BoujeeEnjinia1701/pvtrace/cad/drawings/PVT-DWG-001.pdf

CONCEPT, NOT FOR FABRICATION | PVTrace · github.com/BoujeeEnjinia1701/pvtrace

FRONT VIEW
Scale 1:5; looking at the front (along +Y)

TOP VIEW
Scale 1:5; looking down (along -Z)

RIGHT VIEW
Scale 1:5; looking at the right side (along -X)

320

144 98

ISOMETRIC VIEW
Not to scale; seen from the front right and above, about 30 deg elevation

KEY DIMENSIONS AND INTERFACES (MM)
Case 220 x 130 x 80; 234 x 144 over bumpers
Wall 3; parting line Z 52; knob and hood top Z 98
+X end: 2 x M16 glands at Y +/-18, Z 30, test leads 4 mm2 -X end: M12 sensor gland Y 45; USB-C socket Y 22 Chassis plate PC 1.5 on five 5 mm standoffs
Load: 3 x 2200 uF 160 V, 6.6 mF, 2 cable ties
Isolation board between measurement side and controller
Lid: 3-key membrane keypad and two status LEDs, controller side Window 72 x 54 bonded over 62 x 46 opening
Display board on 4 spacers; hood screws hold both
Rating 100 V DC, 20 A; 20 A gPV fuse; 2-pole DC isolator
Stored energy up to 33 J; dump 22 ohm, bleed 10 kohm Mass about 1.49 kg with leads and pod (PVT-CAL-001) Making sketches PVT-DWG-101 to 108 (lid: 104) PRELIMINARY, NOT FOR FABRICATION
REV | DESCRIPTION | DATE | BY
P1 | Preliminary GA, 6.6 mF and isolation barrier (PVT-DDR-001) | 2026-09-25 | AC
P2 | Display sun hood added (PVT-DDR-002) | 2026-09-25 | AC
P3 | Constructable design: plate, fixings, USB-C (PVT-DDR-003) | 2026-10-01 | AC
P4 | Keypad and status LEDs on the lid (PVT-DEC-001 item 6) | 2026-10-02 | AC
PVTRACE | github.com/BoujeeEnjinia1701/pvtrace

## General arrangement, handheld tracer

DRAWING NO.
PVT-DWG-001

REV
P4

SHEET
1 of 1

SIZE

## ANSI B

SCALE
1:5

UNITS
mm
PROJECTION | DATE
2026-10-02

DRAWN
Amish Chadha

MATERIAL / NOTES
Case IP54 ABS, light grey; window and chassis plate PC; hood PETG. See bom/bom.csv, PVT-CAL-001
Licensed CERN-OHL-S-2.0 · Design Molecule Lab · designmolecule.com | Generated from cad/src; do not edit by hand
