BoujeeEnjinia1701/pvtrace/cad/drawings/PVT-DWG-101.pdf

### BUILD PLAN SKETCH, PLAN NOT YET BUILT PVTrace · github.com/BoujeeEnjinia1701/pvtrace

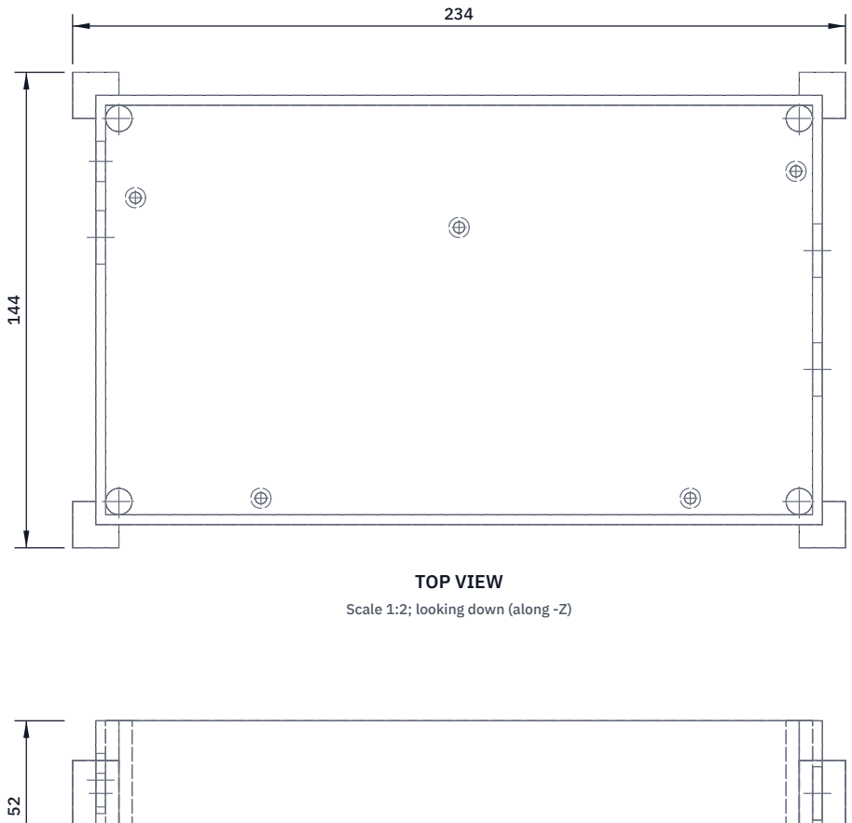
[picture p39: figure]
TOP VIEW; Scale 1:2; looking down (along -Z)

FRONT VIEW
Scale 1:2; looking at the front (along +Y)

RIGHT VIEW
Scale 1:2; looking at the right side (along -X)

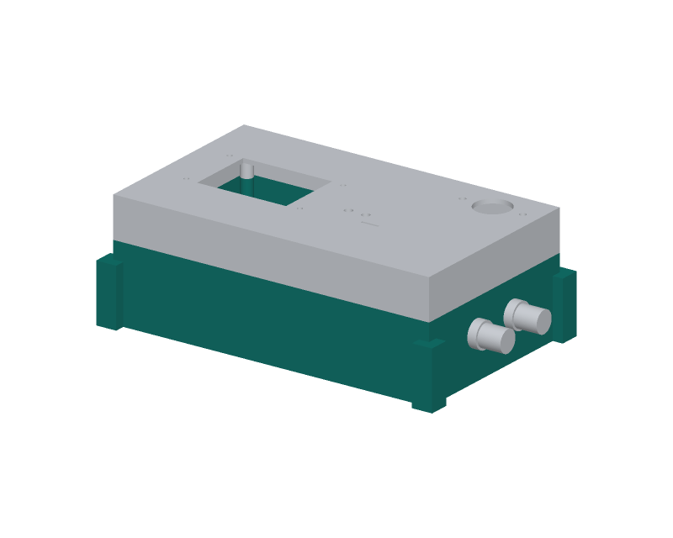
[picture p40: figure]

WHERE IT GOES
This part in colour, its neighbours in grey

HOW TO MAKE IT AND HOW IT FITS
Drill the body only. Front is the long side toward the user; right is
the end the test leads leave from. Sizes from outside faces.
Right end: two 16.2 mm holes for the M16 lead glands, 47 and 83 mm from the front face, 30 mm up from the bottom.
Left end: 16.2 mm hole for the USB-C socket, 87 mm from the front face, 34 mm up; 12.2 mm hole for the M12 sensor gland, 110 mm from the front face, 30 mm up.
Floor: five 3.4 mm holes, countersunk from below for M3 screws, at the positions on the case hole layout (from the left end and front face). Tape each face, pilot drill 2 mm with wood behind, open with a step drill at low speed. Deburr inside and out.
Check: the glands, socket and plate standoffs fit their holes.
REV | DESCRIPTION | DATE | BY
P1 | Making sketch for the prototype build plan | 2026-10-02 | AC
PVTRACE | github.com/BoujeeEnjinia1701/pvtrace

## PVTrace enclosure body: drilling sketch

DRAWING NO.
PVT-DWG-101

REV
P1

SHEET
1 of 1

SIZE

## ANSI B

SCALE
1:2

UNITS
mm
PROJECTION | DATE
2026-10-02

DRAWN
Amish Chadha

MATERIAL / NOTES
Bought IP54 ABS handheld case 220 x 130 x 80 mm, light grey
Licensed CERN-OHL-S-2.0 · Design Molecule Lab · designmolecule.com | Generated from cad/src; do not edit by hand
