BoujeeEnjinia1701/pvtrace/cad/drawings/PVT-DWG-102.pdf

### BUILD PLAN SKETCH, PLAN NOT YET BUILT PVTrace · github.com/BoujeeEnjinia1701/pvtrace

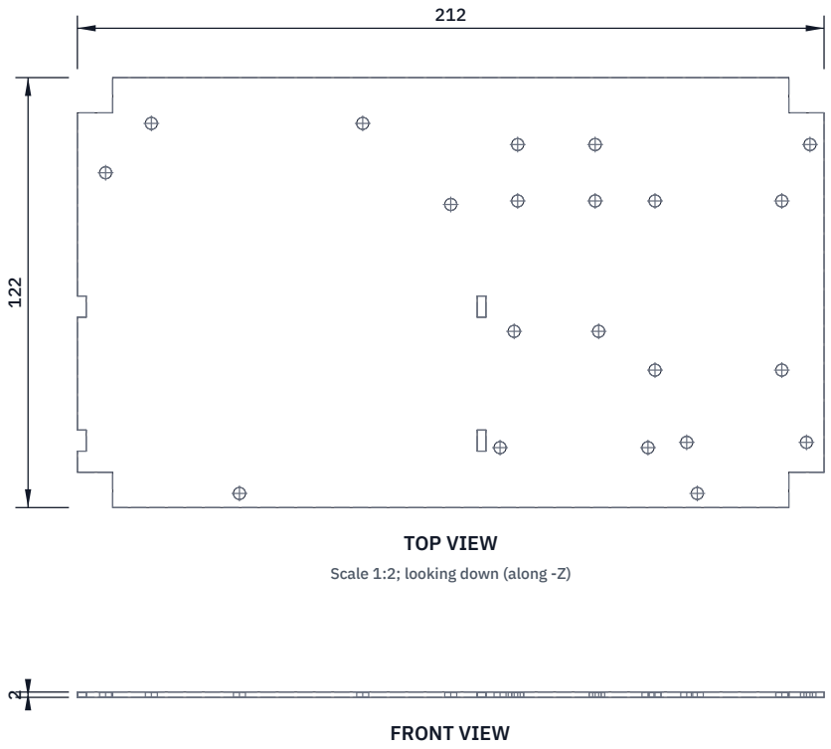
[picture p41: figure]
FRONT VIEW; TOP VIEW; Scale 1:2; looking down (along -Z)

Scale 1:2; looking at the front (along +Y)

RIGHT VIEW
Scale 1:2; looking at the right side (along -X)

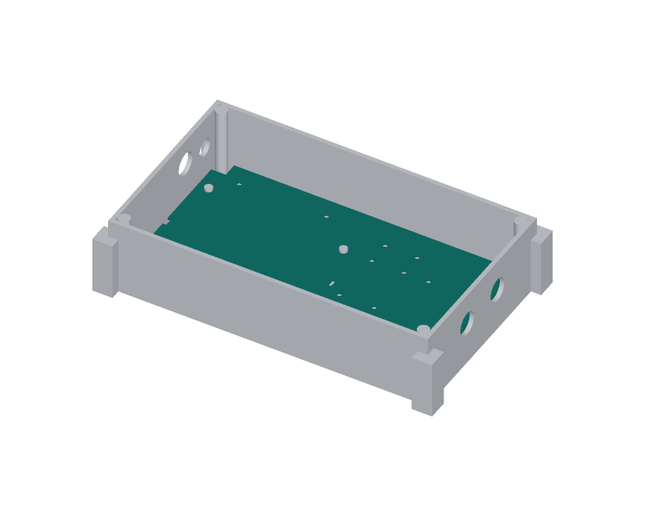
[picture p42: figure]

WHERE IT GOES
This part in colour, its neighbours in grey

HOW TO MAKE IT AND HOW IT FITS
Cut a 212 x 122 mm blank from 1.5 mm polycarbonate; keep the film on. Cut a 10 x 10 mm notch at each corner (clears the lid screw pillars).
Cut four cable tie slots, 2.5 x 6 mm: two open notches on the left edge and two slots 113.5 to 116 mm from the left edge; all four centred
19 and 57 mm from the front edge.
Drill the 21 holes 3.4 mm at the positions on the plate hole layout: five for the standoffs, the rest for the parts on the plate.
Score and snap or saw with a fine blade; file the edges smooth. Fit: the plate sits on five 5 mm standoffs, 1 mm in from every wall. Every part is screwed to the plate before it goes into the case. Check: lay it in the case; it drops in flat past the corner pillars.
REV | DESCRIPTION | DATE | BY
P1 | Making sketch for the prototype build plan | 2026-10-02 | AC
PVTRACE | github.com/BoujeeEnjinia1701/pvtrace

## PVTrace chassis plate: making sketch

DRAWING NO.
PVT-DWG-102

REV
P1

SHEET
1 of 1

SIZE

## ANSI B

SCALE
1:2

UNITS
mm
PROJECTION | DATE
2026-10-02

DRAWN
Amish Chadha

MATERIAL / NOTES
Polycarbonate sheet 1.5 mm, clear
Licensed CERN-OHL-S-2.0 · Design Molecule Lab · designmolecule.com | Generated from cad/src; do not edit by hand
