BoujeeEnjinia1701/pvtrace/cad/drawings/PVT-DWG-103.pdf

### BUILD PLAN SKETCH, PLAN NOT YET BUILT PVTrace · github.com/BoujeeEnjinia1701/pvtrace

FRONT VIEW
Scale 2:1; looking at the front (along +Y)

TOP VIEW
Scale 2:1; looking down (along -Z)

RIGHT VIEW
Scale 2:1; looking at the right side (along -X)

40

10 25

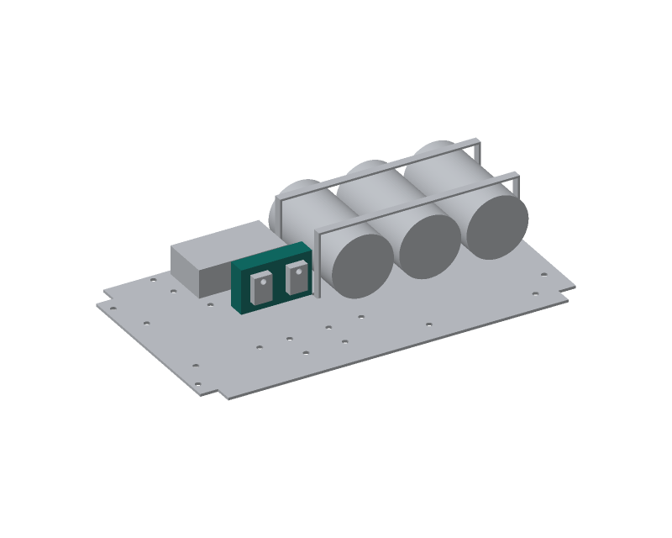
[picture p43: figure]

WHERE IT GOES
This part in colour, its neighbours in grey

HOW TO MAKE IT AND HOW IT FITS
Cut 40 mm off 25 x 10 mm flat bar; square and deburr the ends.
The bar stands on a 40 x 10 mm face (the bottom), 25 mm tall. Bottom: drill 2.5 mm, 9 mm deep, and tap M3 8 deep, 12 mm each side of centre, on the centre line. Screws come up through the plate.
Back face (the 40 x 25 face toward the back of the case): drill
2.5 mm, 7 deep, and tap M3 6 deep, 10 mm each side of centre and 18 mm up from the bottom. One MOSFET tab is screwed to each. File the back face flat; no burrs may pierce the insulating pad.
Fit: each MOSFET tab on an insulating thermal pad, with an insulating bushing under the screw head. The tabs are live at PV voltage. Check: with the MOSFETs fitted, a meter reads open circuit from each tab to the bar.
REV | DESCRIPTION | DATE | BY
P1 | Making sketch for the prototype build plan | 2026-10-02 | AC
PVTRACE | github.com/BoujeeEnjinia1701/pvtrace

## PVTrace MOSFET bar: making sketch

DRAWING NO.
PVT-DWG-103

REV
P1

SHEET
1 of 1

SIZE

## ANSI B

SCALE
2:1

UNITS
mm
PROJECTION | DATE
2026-10-02

DRAWN
Amish Chadha

MATERIAL / NOTES
Aluminium flat bar 25 x 10 mm, 6061 or 6082
Licensed CERN-OHL-S-2.0 · Design Molecule Lab · designmolecule.com | Generated from cad/src; do not edit by hand
