BoujeeEnjinia1701/pvtrace/cad/drawings/PVT-DWG-104.pdf

### BUILD PLAN SKETCH, PLAN NOT YET BUILT PVTrace · github.com/BoujeeEnjinia1701/pvtrace

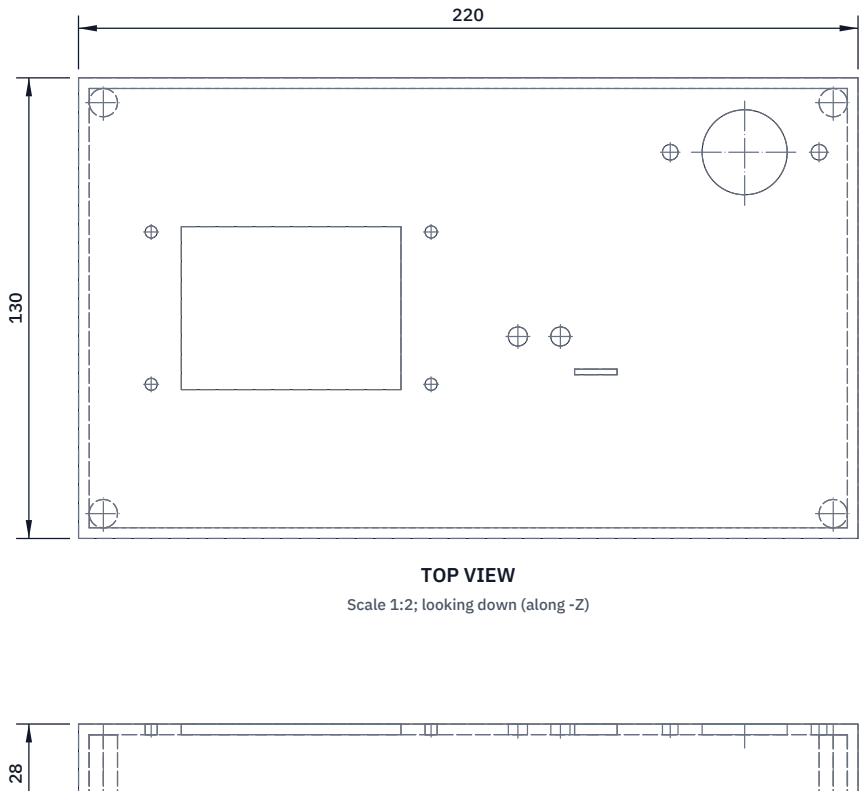
[picture p44: figure]
TOP VIEW; Scale 1:2; looking down (along -Z)

FRONT VIEW
Scale 1:2; looking at the front (along +Y)

RIGHT VIEW
Scale 1:2; looking at the right side (along -X)

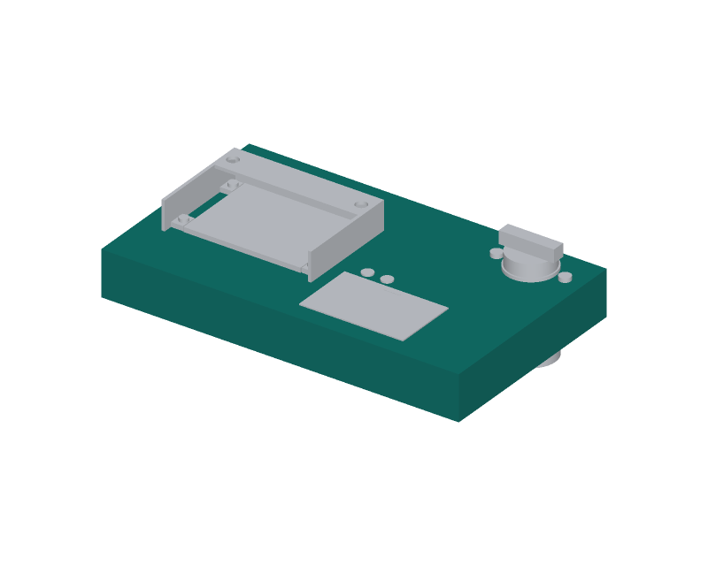
[picture p45: figure]

WHERE IT GOES
This part in colour, its neighbours in grey

HOW TO MAKE IT AND HOW IT FITS
Positions from the lid's left end and front face, outside, top view. Display opening 62 x 46 mm, centred 60 from the left end and 65 from the front: drill the corners 6 mm, cut between with a fine saw, file. Four 3.4 mm holes for the display screws at 20.5 and 99.5 from the left end, each 43.5 and 86.5 from the front.
DC isolator: 24 mm hole centred 188 from the left end and 109 from the front; two 4.4 mm holes 21 mm each side of it, left and right.
Check the isolator maker's cut-out before cutting; follow it if it differs. Keypad tail slot 12 x 1.6 mm, centred 146 from the left end and 47 from the front (long side across). Two 5.4 mm LED holes at 124 and 136 from the left end, each 57 from the front. The keypad itself is bonded on. Tape the face, cut slowly, deburr; clean with soap and water.
Check: the window covers the opening with 4 to 5 mm all round; the hood's four tabs line up with the four small holes.
REV | DESCRIPTION | DATE | BY
P1 | Making sketch for the prototype build plan | 2026-10-02 | AC
PVTRACE | github.com/BoujeeEnjinia1701/pvtrace

## PVTrace lid: cutting and drilling sketch

DRAWING NO.
PVT-DWG-104

REV
P1

SHEET
1 of 1

SIZE

## ANSI B

SCALE
1:2

UNITS
mm
PROJECTION | DATE
2026-10-02

DRAWN
Amish Chadha

MATERIAL / NOTES
Lid of the bought case, ABS 3 mm
Licensed CERN-OHL-S-2.0 · Design Molecule Lab · designmolecule.com | Generated from cad/src; do not edit by hand
