BoujeeEnjinia1701/pvtrace/cad/drawings/PVT-DWG-105.pdf

### BUILD PLAN SKETCH, PLAN NOT YET BUILT PVTrace · github.com/BoujeeEnjinia1701/pvtrace

FRONT VIEW
Scale 1:1; looking at the front (along +Y)

TOP VIEW
Scale 1:1; looking down (along -Z)

RIGHT VIEW
Scale 1:1; looking at the right side (along -X)

72

54 3

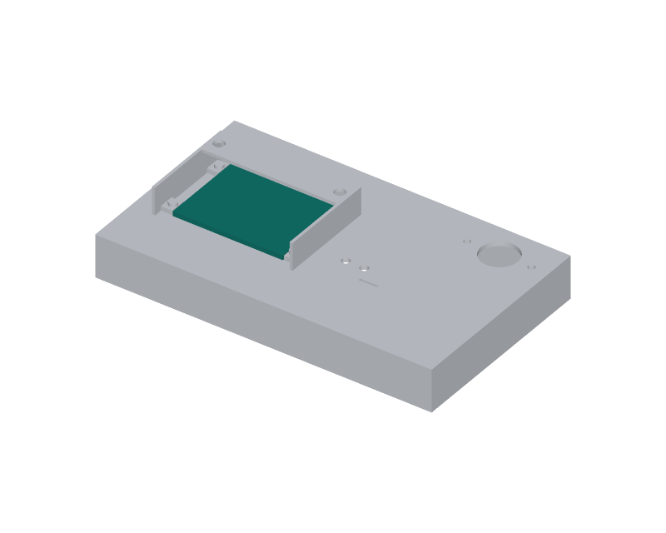
[picture p46: figure]

WHERE IT GOES
This part in colour, its neighbours in grey

HOW TO MAKE IT AND HOW IT FITS
Cut 72 x 54 mm from 3 mm clear polycarbonate; keep the film on both faces until it is bonded.
Score and snap, or saw with a fine blade; file and polish the edges. Break the corners 1 mm so the gasket tape does not lift.
Lay 4 mm wide closed-cell adhesive gasket tape round the underside, on the edge, in one length with a butt joint at the back.
Fit: bonded on top of the lid, centred over the 62 x 46 mm opening, overlapping it 5 mm at the ends and 4 mm at the sides.
The hood's tabs and screws sit just outside its ends, 0.75 mm clear. Check: no gap in the gasket all round; the display reads through it.
REV | DESCRIPTION | DATE | BY
P1 | Making sketch for the prototype build plan | 2026-10-02 | AC
PVTRACE | github.com/BoujeeEnjinia1701/pvtrace

## PVTrace display window: making sketch

DRAWING NO.
PVT-DWG-105

REV
P1

SHEET
1 of 1

SIZE

## ANSI B

SCALE
1:1

UNITS
mm
PROJECTION | DATE
2026-10-02

DRAWN
Amish Chadha

MATERIAL / NOTES
Clear polycarbonate sheet 3 mm
Licensed CERN-OHL-S-2.0 · Design Molecule Lab · designmolecule.com | Generated from cad/src; do not edit by hand
