BoujeeEnjinia1701/pvtrace/cad/drawings/PVT-DWG-106.pdf

### BUILD PLAN SKETCH, PLAN NOT YET BUILT PVTrace · github.com/BoujeeEnjinia1701/pvtrace

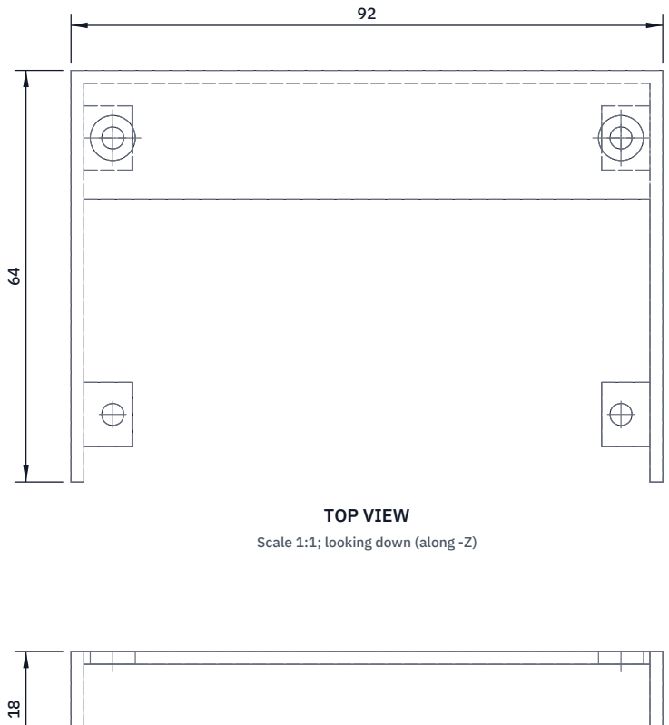
[picture p47: figure]
TOP VIEW; Scale 1:1; looking down (along -Z)

FRONT VIEW
Scale 1:1; looking at the front (along +Y)

RIGHT VIEW
Scale 1:1; looking at the right side (along -X)

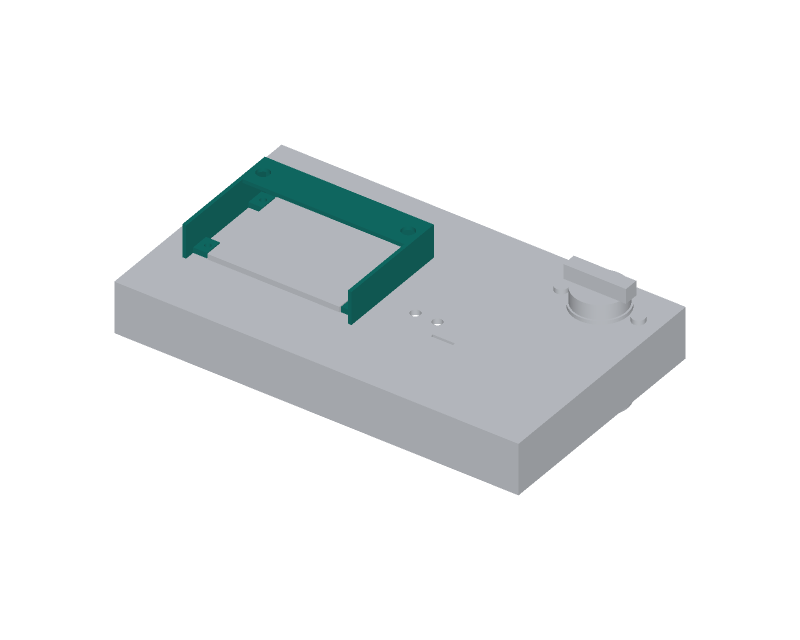
[picture p48: figure]

WHERE IT GOES
This part in colour, its neighbours in grey

HOW TO MAKE IT AND HOW IT FITS
Print in light grey PETG, 0.2 mm layers, 4 walls, 30 % infill,
roof lip down on the bed so the walls need no supports.
Outside 92 x 64 x 18 mm: two side walls and a back wall 2 mm thick, a roof lip 20 mm deep along the back; open at the front (user side). Four tabs inside the side walls, 7.5 x 10 x 3 mm, flush with the bottom edge, centred 21.5 mm each side of the hood's middle.
Tab holes 3.4 mm: 79 mm apart across, 43 mm apart front to back; 7 mm screwdriver holes through the roof lip over the two back tabs. Fit: four M3 x 20 screws with sealing washers pass through the tabs, the lid and the spacers and also hold the display board.
Check: the hood's top is level with the isolator knob top, 98 mm up.
REV | DESCRIPTION | DATE | BY
P1 | Making sketch for the prototype build plan | 2026-10-02 | AC
PVTRACE | github.com/BoujeeEnjinia1701/pvtrace

## PVTrace display sun hood: making sketch

DRAWING NO.
PVT-DWG-106

REV
P1

SHEET
1 of 1

SIZE

## ANSI B

SCALE
1:1

UNITS
mm
PROJECTION | DATE
2026-10-02

DRAWN
Amish Chadha

MATERIAL / NOTES
PETG, 3D printed, light grey
Licensed CERN-OHL-S-2.0 · Design Molecule Lab · designmolecule.com | Generated from cad/src; do not edit by hand
