BoujeeEnjinia1701/pvtrace/cad/drawings/PVT-DWG-107.pdf

### BUILD PLAN SKETCH, PLAN NOT YET BUILT PVTrace · github.com/BoujeeEnjinia1701/pvtrace

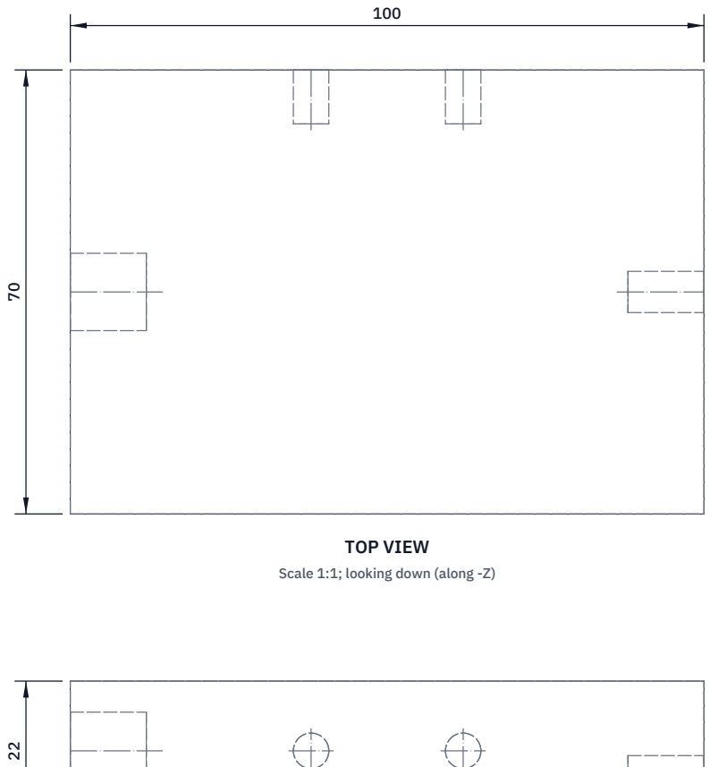
[picture p49: figure]
TOP VIEW; Scale 1:1; looking down (along -Z)

FRONT VIEW
Scale 1:1; looking at the front (along +Y)

RIGHT VIEW
Scale 1:1; looking at the right side (along -X)

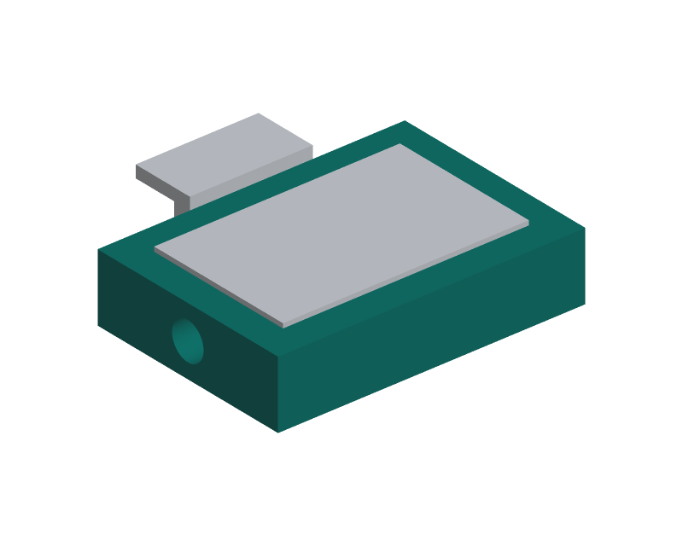
[picture p50: figure]

WHERE IT GOES
This part in colour, its neighbours in grey

HOW TO MAKE IT AND HOW IT FITS
Print 100 x 70 x 22 mm, top face up, 4 walls, 30 % infill, with a
6 mm channel inside from the top centre to the left end hole.
Left end: 12.2 mm hole, 12 deep, centred, for the M12 cable gland. Right end: 6.5 mm hole for the temperature probe lead, 4 mm below centre; fit a rubber grommet.
Clip face (the long side toward the module): two 5.6 mm holes, 8.5 deep, 12 mm each side of centre, mid height; press in M4 heat-set inserts with a soldering iron.
Bond the reference cell centred on the top face with neutral-cure silicone; lead its wires down the channel and seal the channel. Check: the cell face is flat and parallel to the housing base.
REV | DESCRIPTION | DATE | BY
P1 | Making sketch for the prototype build plan | 2026-10-02 | AC
PVTRACE | github.com/BoujeeEnjinia1701/pvtrace

## PVTrace sensor pod housing: making sketch

DRAWING NO.
PVT-DWG-107

REV
P1

SHEET
1 of 1

SIZE

## ANSI B

SCALE
1:1

UNITS
mm
PROJECTION | DATE
2026-10-02

DRAWN
Amish Chadha

MATERIAL / NOTES
PETG or ASA, 3D printed, light grey
Licensed CERN-OHL-S-2.0 · Design Molecule Lab · designmolecule.com | Generated from cad/src; do not edit by hand
