BoujeeEnjinia1701/pvtrace/cad/drawings/PVT-DWG-108.pdf

### BUILD PLAN SKETCH, PLAN NOT YET BUILT PVTrace · github.com/BoujeeEnjinia1701/pvtrace

FRONT VIEW
Scale 1:1; looking at the front (along +Y)

TOP VIEW
Scale 1:1; looking down (along -Z)

RIGHT VIEW
Scale 1:1; looking at the right side (along -X)

40

21 52

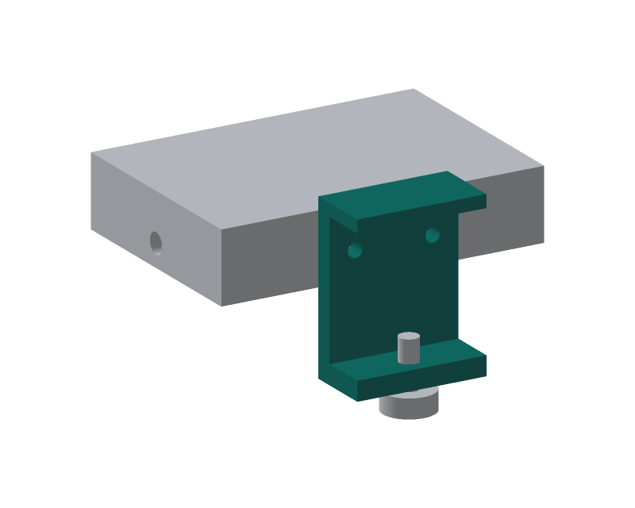
[picture p51: figure]

WHERE IT GOES
This part in colour, its neighbours in grey

HOW TO MAKE IT AND HOW IT FITS
Print on its side, 100 % infill: a C shape 40 mm wide, 21 mm deep and 52 mm tall; back 6 mm, top jaw 4 mm, bottom jaw 6 mm thick.
Opening between the jaws 42 mm, for module frames 30 to 40 mm deep. Bottom jaw: 6.6 mm hole 14 mm in from the back face, centred; an M6 nut sits in a hex pocket on top, or tap the jaw M6 directly.
Back: two 4.4 mm holes, 12 mm each side of centre, 15 mm below the top; two M4 x 12 screws go into the housing's inserts.
Fit: the top jaw rests on the frame's top edge and the thumb screw presses up under the frame's bottom flange; the cell then lies about 4 mm above the glass and parallel to it.
Check: on a frame offcut, the pod cannot rock when the screw is snug.
REV | DESCRIPTION | DATE | BY
P1 | Making sketch for the prototype build plan | 2026-10-02 | AC
PVTRACE | github.com/BoujeeEnjinia1701/pvtrace

## PVTrace sensor pod clip: making sketch

DRAWING NO.
PVT-DWG-108

REV
P1

SHEET
1 of 1

SIZE

## ANSI B

SCALE
1:1

UNITS
mm
PROJECTION | DATE
2026-10-02

DRAWN
Amish Chadha

MATERIAL / NOTES
PETG or ASA, 3D printed, 100 % infill
Licensed CERN-OHL-S-2.0 · Design Molecule Lab · designmolecule.com | Generated from cad/src; do not edit by hand
