BoujeeEnjinia1701/pvtrace/cad/drawings/PVT-DWG-001.png

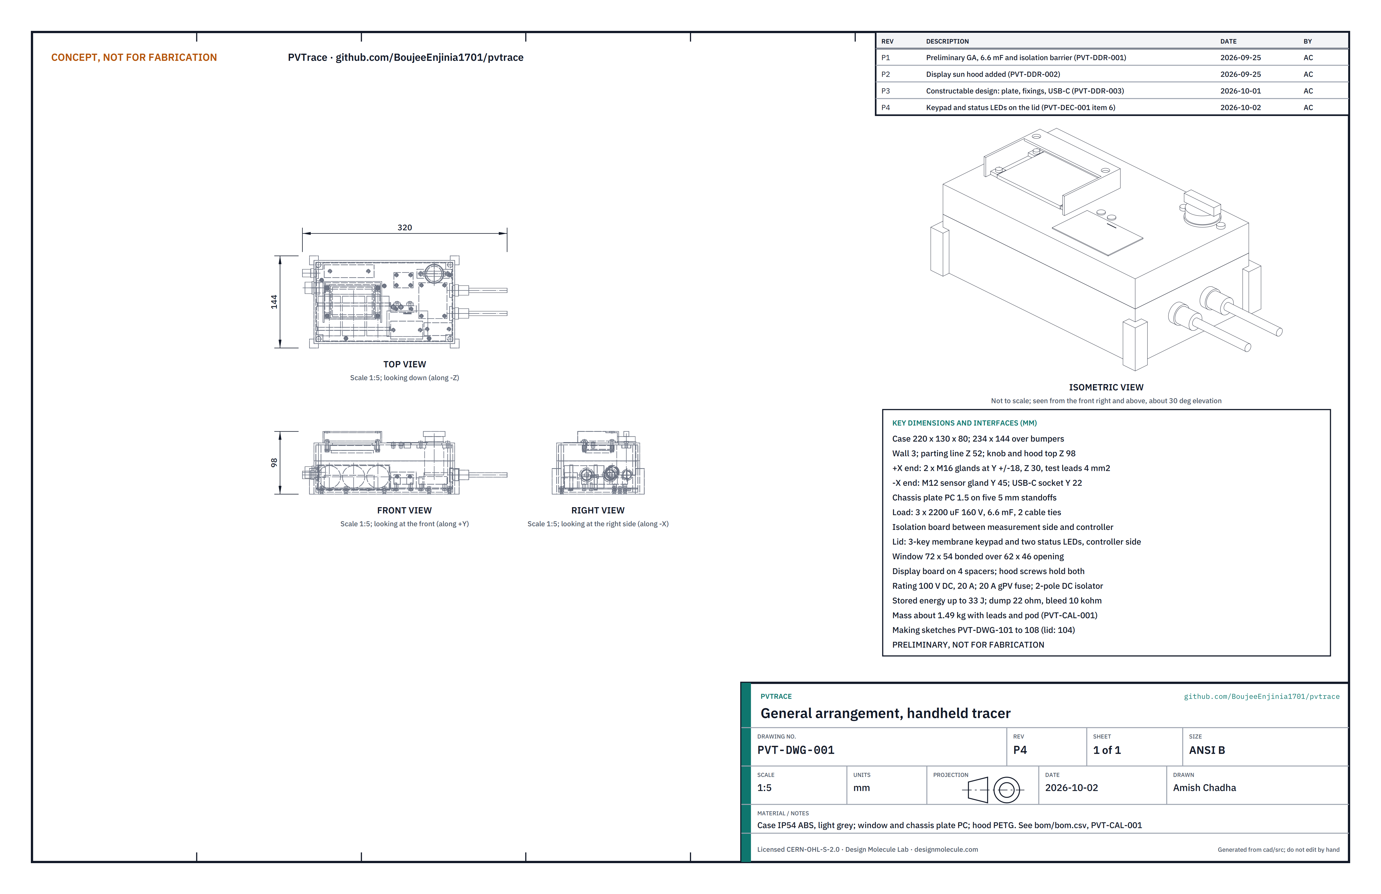
cad/drawings/PVT-DWG-001.png
