BoujeeEnjinia1701/pvtrace/media/card.png

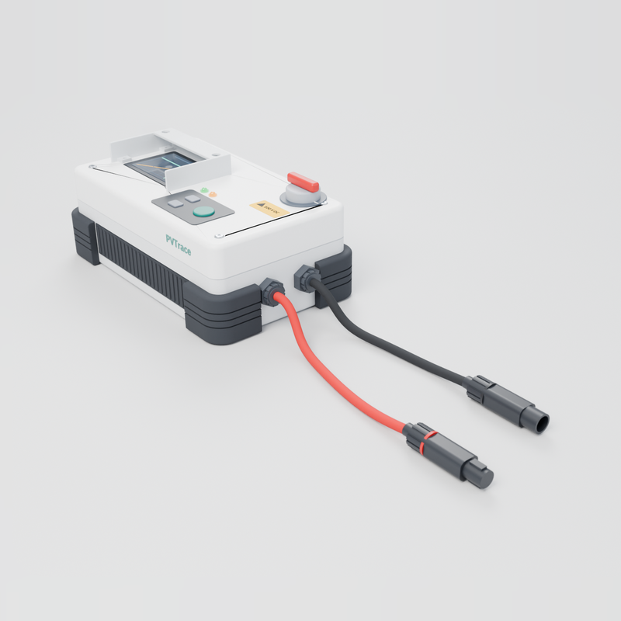
media/card.png
