BoujeeEnjinia1701/pvtrace/media/render-exploded.png

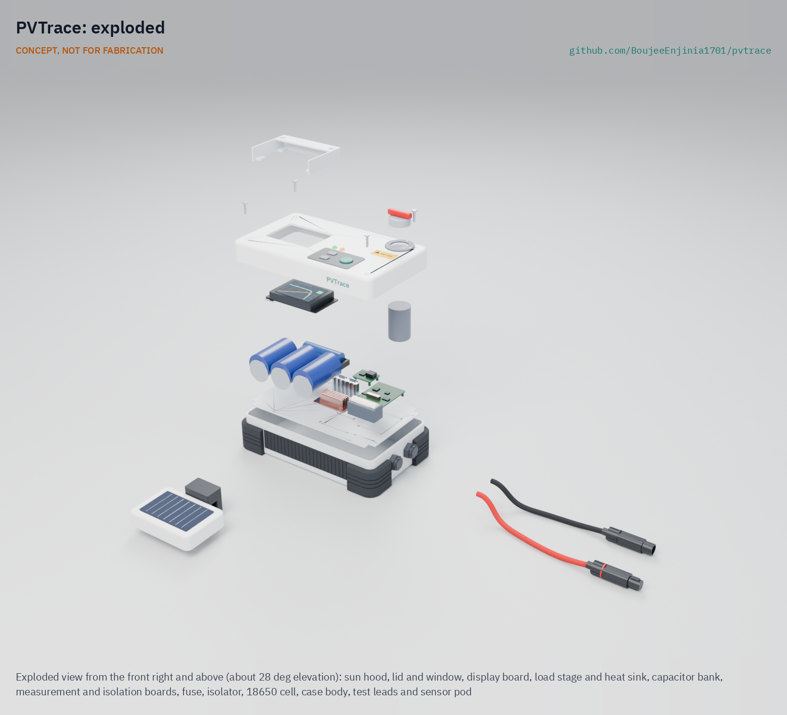
media/render-exploded.png
