BoujeeEnjinia1701/pvtrace/media/render-in-use.png

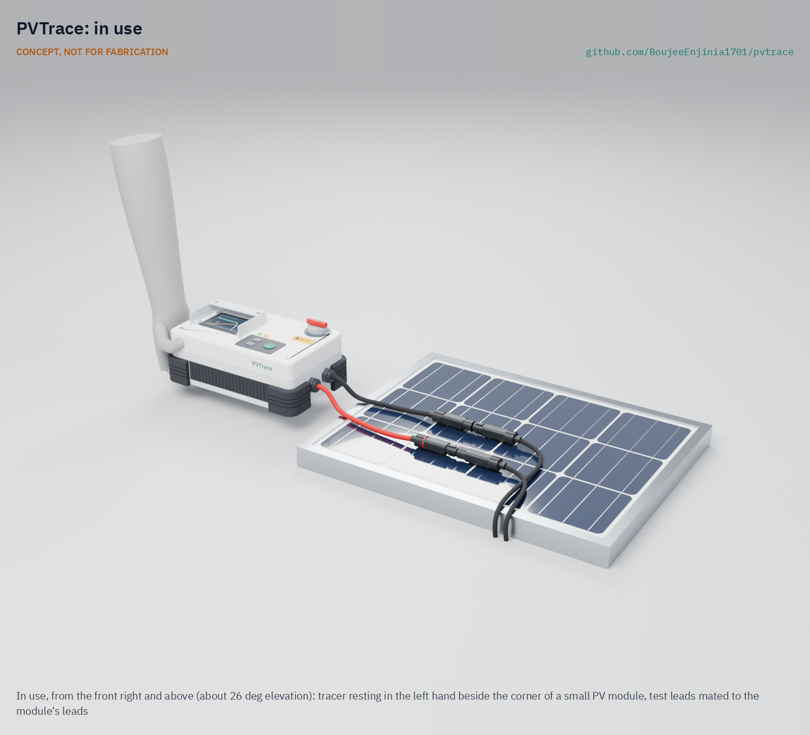
media/render-in-use.png
