BoujeeEnjinia1701/pvtrace/media/social-preview.png

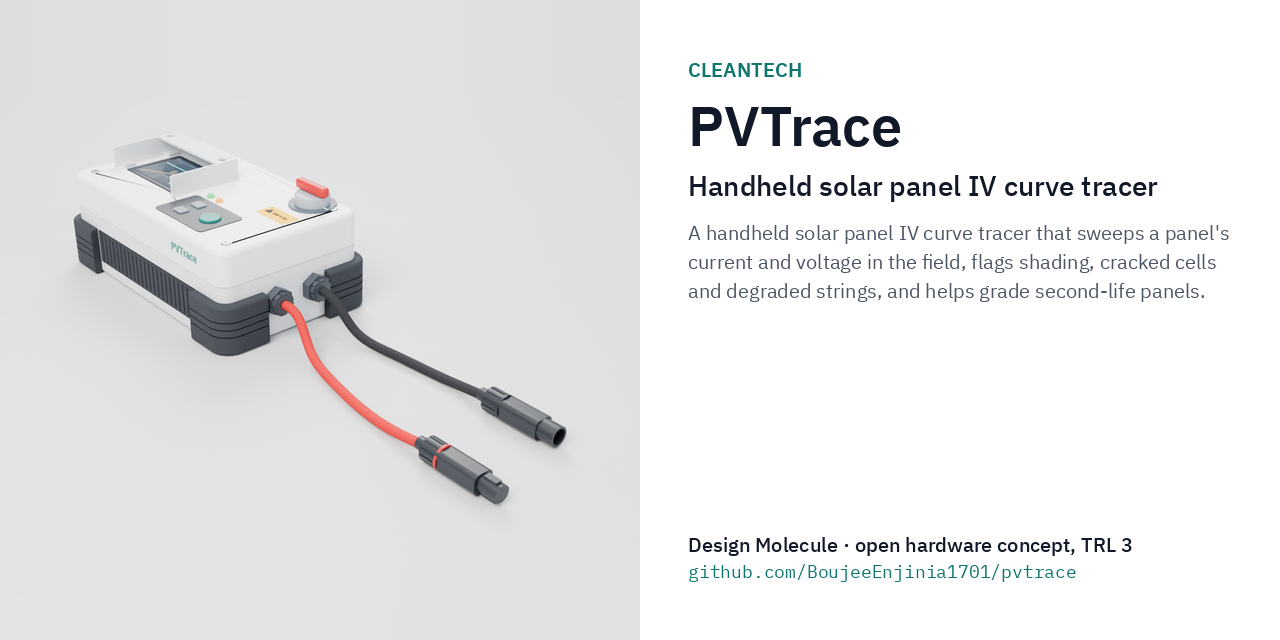
media/social-preview.png
